itsahmedkhalil/SixDOFRoboticController/src/data_to_pose/scripts/imudata.py

#!/usr/bin/env python
# license removed for brevity
from itertools import count
import rospy
import serial
import os
from time import time
import matplotlib.pyplot as plt
import numpy as np
import pandas as pd
from rospy import Time
from scipy.spatial.transform import Rotation as R
import random
from geometry_msgs.msg import Quaternion, Twist, Vector3
import sys
""" Appends the path of openzen.so NEED TO CHANGE DIRECTORY or just add the openzen.so into the scripts directory"""
sys.path.append('/home/mohamed/openzen/build')
# sys.path.append('/home/ahmedkhalil/openzen')
import openzen


def main(): 
    """
    This function finds the LPMS IMU, reads the sensor data, and publishes the quaternion and gyro data
    at a rate of 400 Hz
    """
    imuPub = rospy.Publisher("/imu_data", Quaternion, queue_size=2)
    angVelPub = rospy.Publisher("/gyr_data", Vector3, queue_size=2)
    angVel = Vector3()
    rospy.init_node("imu_publisher")
    rate = rospy.Rate(400)
    counter = 0
    quat_init = np.array([1,0,0,0])
    imu_angle = Quaternion()
    imu_angle.x = 0
    imu_angle.y = 0
    imu_angle.z = 0
    imu_angle.w = 1
    openzen.set_log_level(openzen.ZenLogLevel.Warning)

    error, client = openzen.make_client()
    if not error == openzen.ZenError.NoError:
        print ("Error while initializing OpenZen library")
        sys.exit(1)

    error = client.list_sensors_async()

    # check for events
    sensor_desc_connect = None
    while True:
        zenEvent = client.wait_for_next_event()

        if zenEvent.event_type == openzen.ZenEventType.SensorFound:
            print ("Found sensor {} on IoType {}".format( zenEvent.data.sensor_found.name,
                zenEvent.data.sensor_found.io_type))
            if sensor_desc_connect is None:
                sensor_desc_connect = zenEvent.data.sensor_found

        if zenEvent.event_type == openzen.ZenEventType.SensorListingProgress:
            lst_data = zenEvent.data.sensor_listing_progress
            print ("Sensor listing progress: {} %".format(lst_data.progress * 100))
            if lst_data.complete > 0:
                break
    print ("Sensor Listing complete")

    if sensor_desc_connect is None:
        print("No sensors found")
        sys.exit(1)

    # connect to the first sensor found
    error, sensor = client.obtain_sensor(sensor_desc_connect)

    # or connect to a sensor by name
    #error, sensor = client.obtain_sensor_by_name("LinuxDevice", "LPMSCU2000003")

    if not error == openzen.ZenSensorInitError.NoError:
        print ("Error connecting to sensor")
        sys.exit(1)

    print ("Connected to sensor !")

    imu = sensor.get_any_component_of_type(openzen.component_type_imu)
    if imu is None:
        print ("No IMU found")
        sys.exit(1)

    ## read bool property
    error, is_streaming = imu.get_bool_property(openzen.ZenImuProperty.StreamData)
    if not error == openzen.ZenError.NoError:
        print ("Can't load streaming settings")
        sys.exit(1)

    print ("Sensor is streaming data: {}".format(is_streaming))

    while not rospy.is_shutdown():
        #try:
            
        zenEvent = client.wait_for_next_event()

        # check if its an IMU sample event and if it
        # comes from our IMU and sensor component
        if zenEvent.event_type == openzen.ZenEventType.ImuData and \
            zenEvent.sensor == imu.sensor and \
            zenEvent.component.handle == imu.component.handle:

            imu_data = zenEvent.data.imu_data
        
        # the if statement is just for storing the initial orientation of the LPMS 
        if counter > 100:
            quat = np.array(imu_data.q) #comes in as w,x,y,z
            gyr = np.array(imu_data.g)
            quat = np.array([quat[1], quat[2],quat[3],quat[0]]) # want in x,y,z,w order
            rot = R.from_quat(quat).inv()   #The LPMS inherently gets the inverse orientation
            quat = rot.as_quat()

            quat_new = quaternion_multiply(quat_init,quat) #=(q_init_wrt_g)^-1 * q_sensor_wrt_g

            imu_angle.w = quat_new[3]
            imu_angle.x = quat_new[0]
            imu_angle.y = quat_new[1]
            imu_angle.z = quat_new[2]

            angVel.x = gyr[0]*np.pi/180.0
            angVel.y = gyr[1]*np.pi/180.0
            angVel.z = gyr[2]*np.pi/180.0
            
            imuPub.publish(imu_angle)
            angVelPub.publish(angVel)
        

        else:
            quat_init = np.array(imu_data.q)    #quaternion of initial frame wrt global frame ;comes in as w,x,y,z
            quat_init = np.array([quat_init[1], quat_init[2],quat_init[3],quat_init[0]]) # want in x,y,z,w order
            rot_init = R.from_quat(quat_init)#.inv()   #rotation matrix of global wrt initial frame
            quat_init = rot_init.as_quat()
            print(quat_init)     #The LPMS inherently gets the inverse orientation
            print(counter)
            counter +=1

            
        # except rospy.ROSInterruptException:
        #     pass
        rate.sleep()
    
def quaternion_multiply(quaternion1, quaternion0):
    """Function used for efficiently multiplying two quaternions"""
    x0, y0, z0, w0 = quaternion0
    x1, y1, z1, w1 = quaternion1
    return np.array([x1 * w0 + y1 * z0 - z1 * y0 + w1 * x0,
                -x1 * z0 + y1 * w0 + z1 * x0 + w1 * y0,
                x1 * y0 - y1 * x0 + z1 * w0 + w1 * z0,
                -x1 * x0 - y1 * y0 - z1 * z0 + w1 * w0], dtype=np.float64)


if __name__ == '__main__':
    try:
        main()
    except rospy.ROSInterruptException:
        pass
